Alectardy98/pcb_FXTal_Rev1/meta/firmware/fxtal/keymaps/alec/fxtal-rev2.png

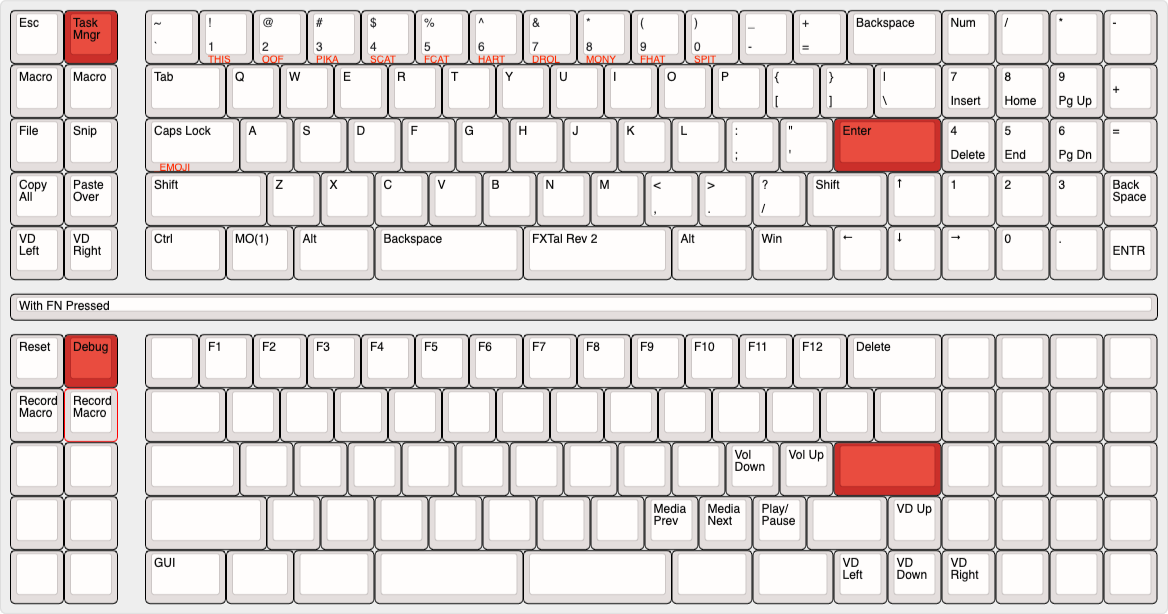
meta/firmware/fxtal/keymaps/alec/fxtal-rev2.png
